lheywang/VolumeMixer/pcb/rev1/untitled.kicad_sch

## KiCad design pcb/rev1/untitled.kicad_sch (2025-06-10)

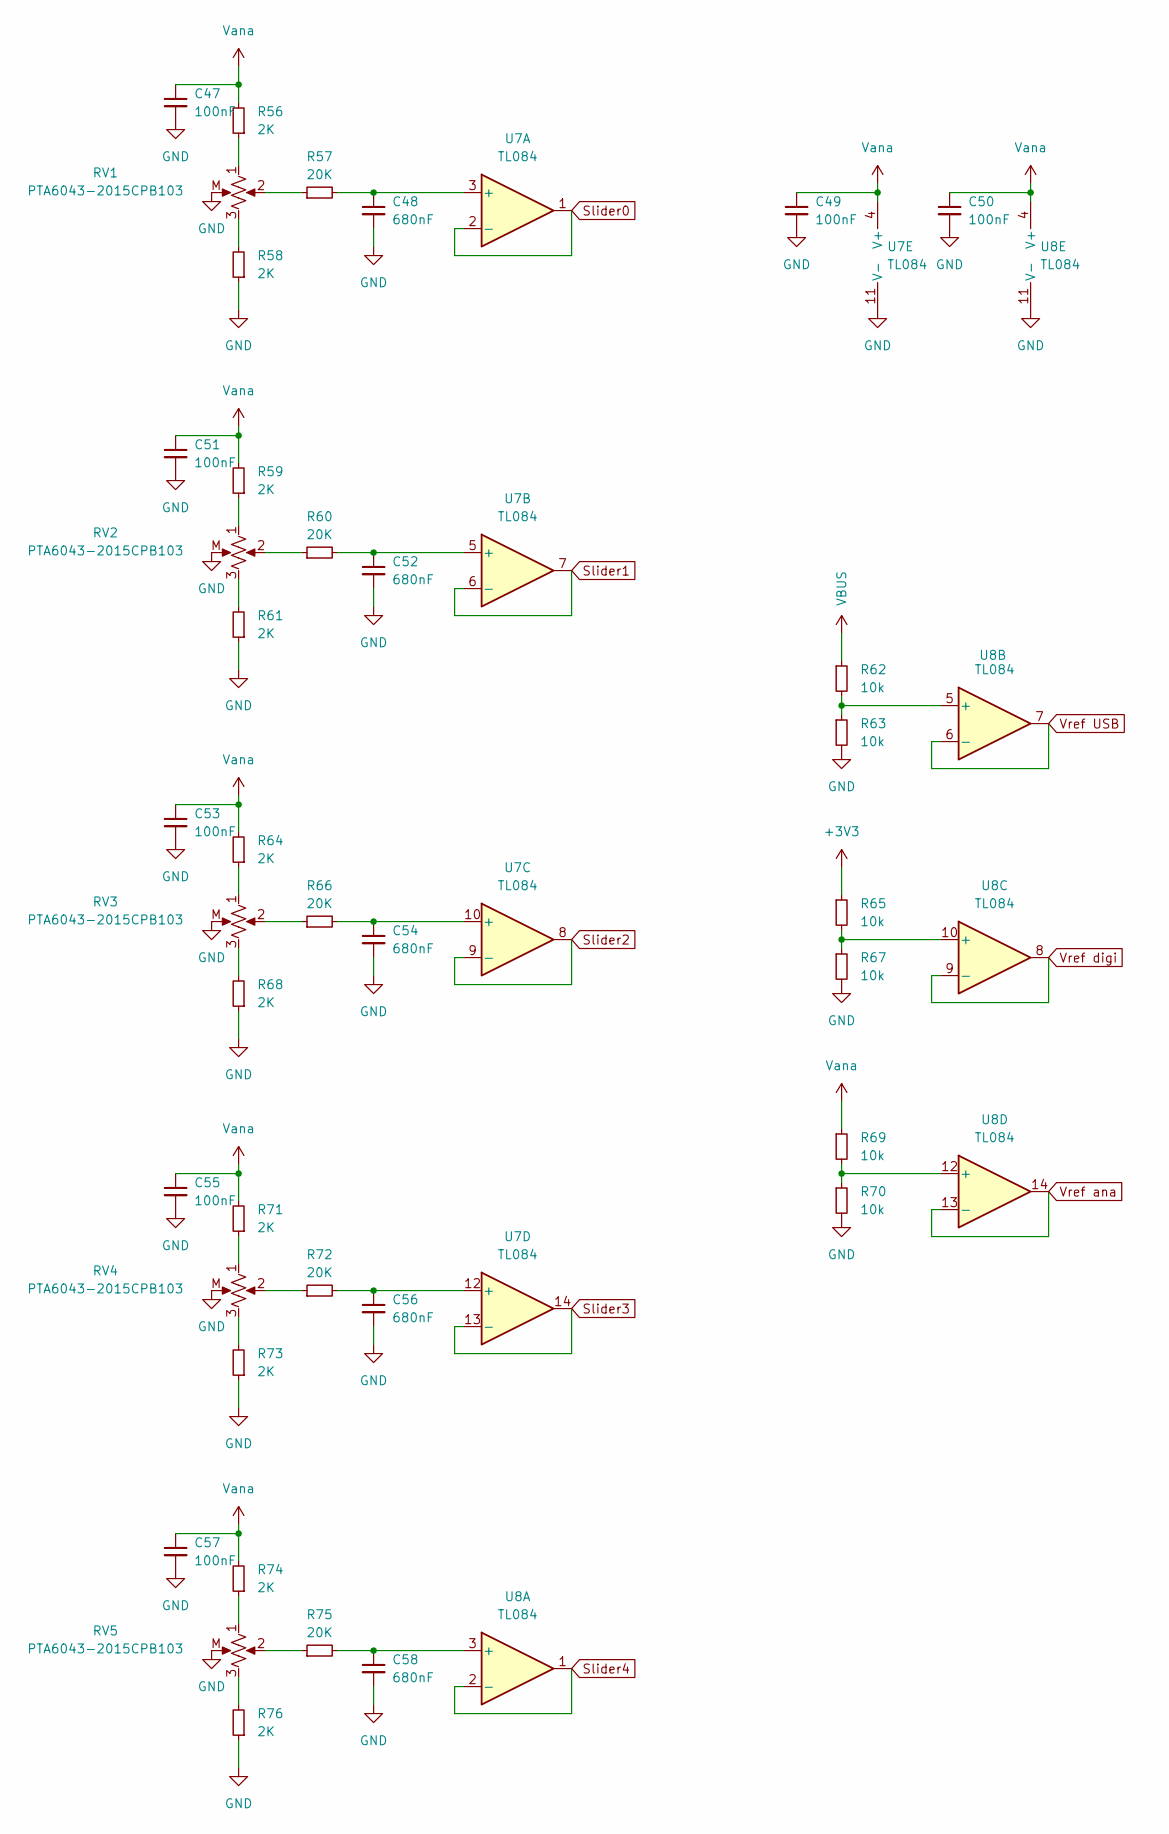
[picture p10: schematic untitled.kicad_sch]

Parts:
C47, C49, C50, C51, C53, C55, C57: 100nF; C_0603_1608Metric
C48, C52, C54, C56, C58: 680nF; C_0603_1608Metric
R56, R58, R59, R61, R64, R68, R71, R73, R74, R76: 2K; R_0603_1608Metric
R57, R60, R66, R72, R75: 20K; R_0603_1608Metric
R62, R63, R65, R67, R69, R70: 10k; R_0603_1608Metric
RV1, RV2, RV3, RV4, RV5: PTA6043-2015CPB103; Slider Bourns PTA6043-2015CPB103
U7, U8: TL084; SOIC-14_3.9x8.7mm_P1.27mm

Connections:
+3V3: R65.1
GND: C47.2, C48.2, C49.2, C50.2, C51.2, C52.2, C53.2, C54.2, C55.2, C56.2, C57.2, C58.2, R58.1, R61.1, R63.2, R67.2, R68.1, R70.2, R73.1, R76.1, RV1.M, RV2.M, RV3.M, RV4.M, RV5.M, U7.11 (V-), U8.11 (V-)
unnamed: C48.1, R57.2, U7.3 (+)
unnamed: C52.1, R60.2, U7.5 (+)
unnamed: C54.1, R66.2, U7.10 (+)
unnamed: C56.1, R72.2, U7.12 (+)
unnamed: C58.1, R75.2, U8.3 (+)
unnamed: R56.1, RV1.1
unnamed: R57.1, RV1.2
unnamed: R58.2, RV1.3
unnamed: R59.1, RV2.1
unnamed: R60.1, RV2.2
unnamed: R61.2, RV2.3
unnamed: R62.2, R63.1, U8.5 (+)
unnamed: R64.1, RV3.1
unnamed: R65.2, R67.1, U8.10 (+)
unnamed: R66.1, RV3.2
unnamed: R68.2, RV3.3
unnamed: R69.2, R70.1, U8.12 (+)
unnamed: R71.1, RV4.1
unnamed: R72.1, RV4.2
unnamed: R73.2, RV4.3
unnamed: R74.1, RV5.1
unnamed: R75.1, RV5.2
unnamed: R76.2, RV5.3
Slider0: U7.1, U7.2 (-)
Slider1: U7.6 (-), U7.7
Slider2: U7.8, U7.9 (-)
Slider3: U7.13 (-), U7.14
Slider4: U8.1, U8.2 (-)
VBUS: R62.1
Vana: C47.1, C49.1, C50.1, C51.1, C53.1, C55.1, C57.1, R56.2, R59.2, R64.2, R69.1, R71.2, R74.2, U7.4 (V+), U8.4 (V+)
Vref USB: U8.6 (-), U8.7
Vref ana: U8.13 (-), U8.14
Vref digi: U8.8, U8.9 (-)
