lheywang/VolumeMixer/pcb/rev1/volume-mixer.kicad_sch

## KiCad design pcb/rev1/volume-mixer.kicad_sch (2025-06-10)

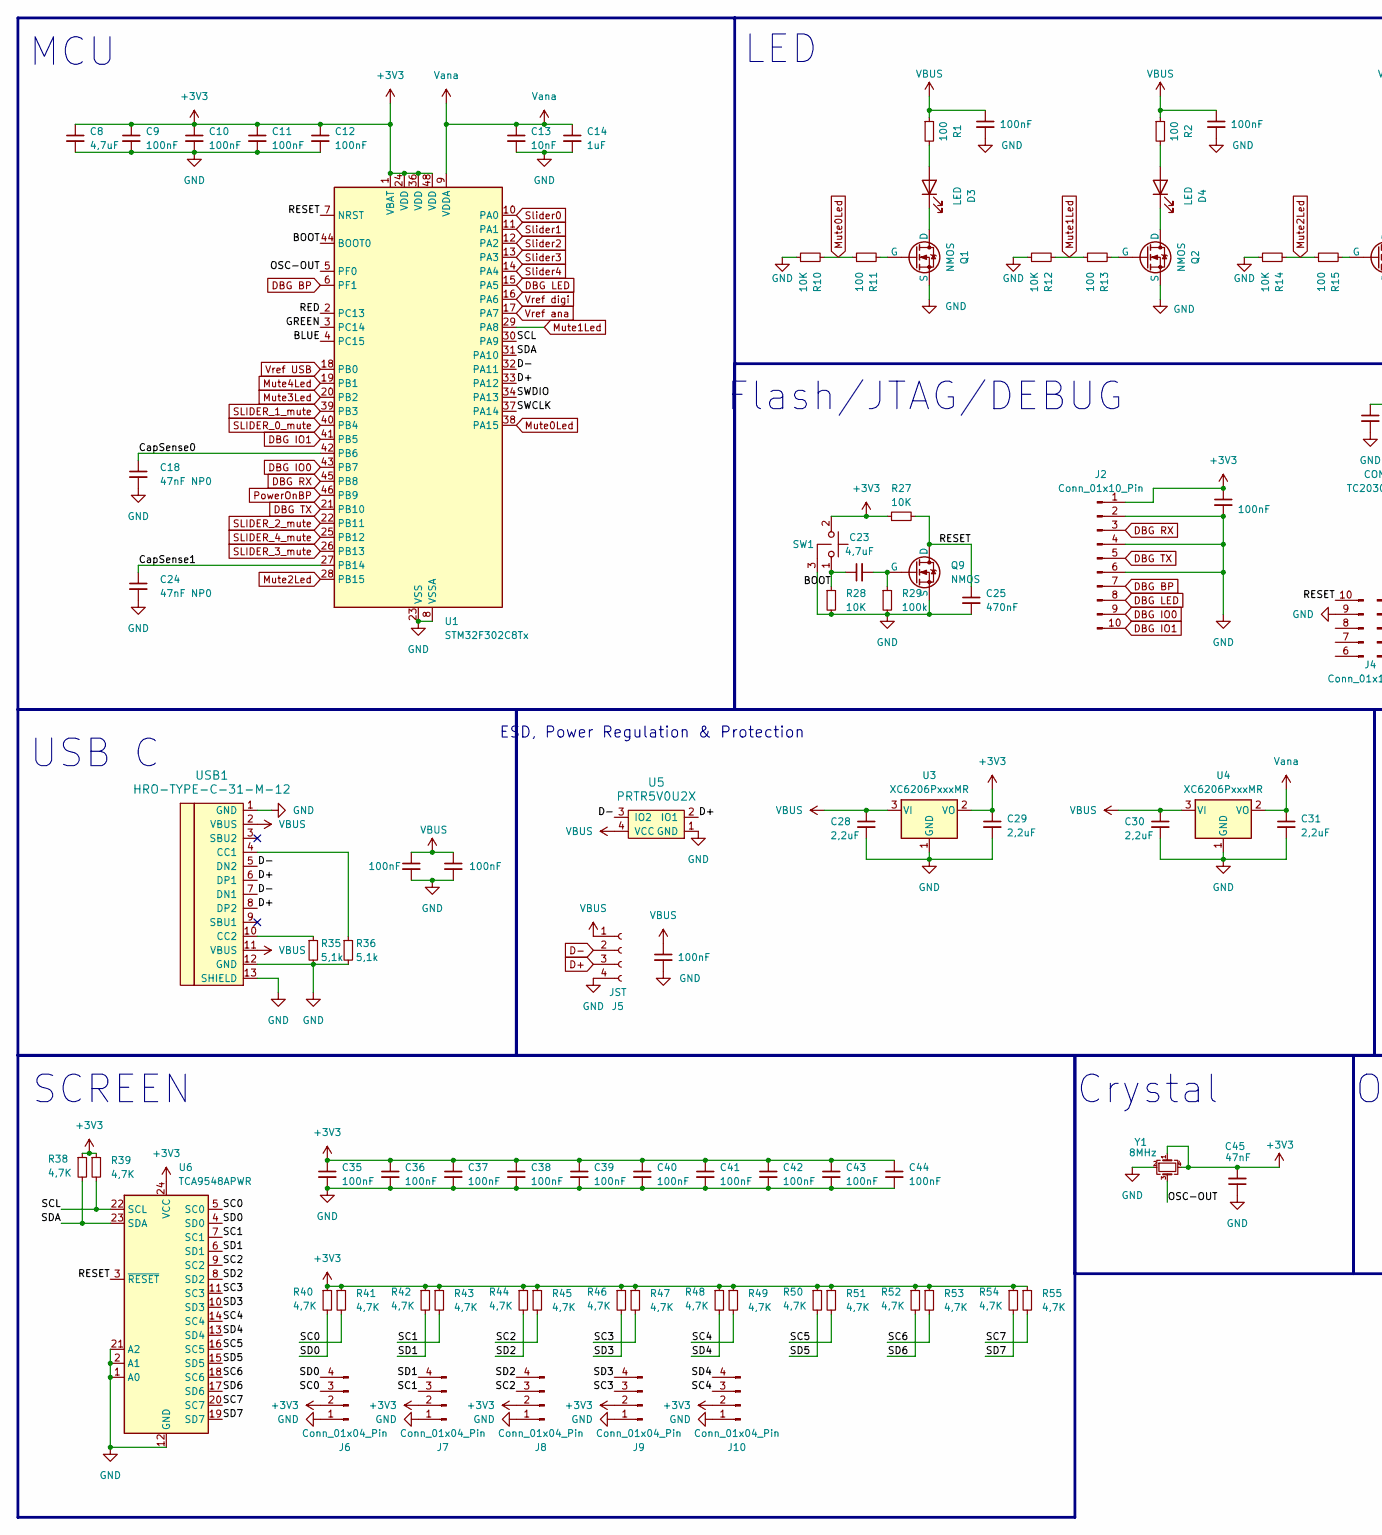
[picture p11: schematic volume-mixer.kicad_sch, part in row 1, column 1]

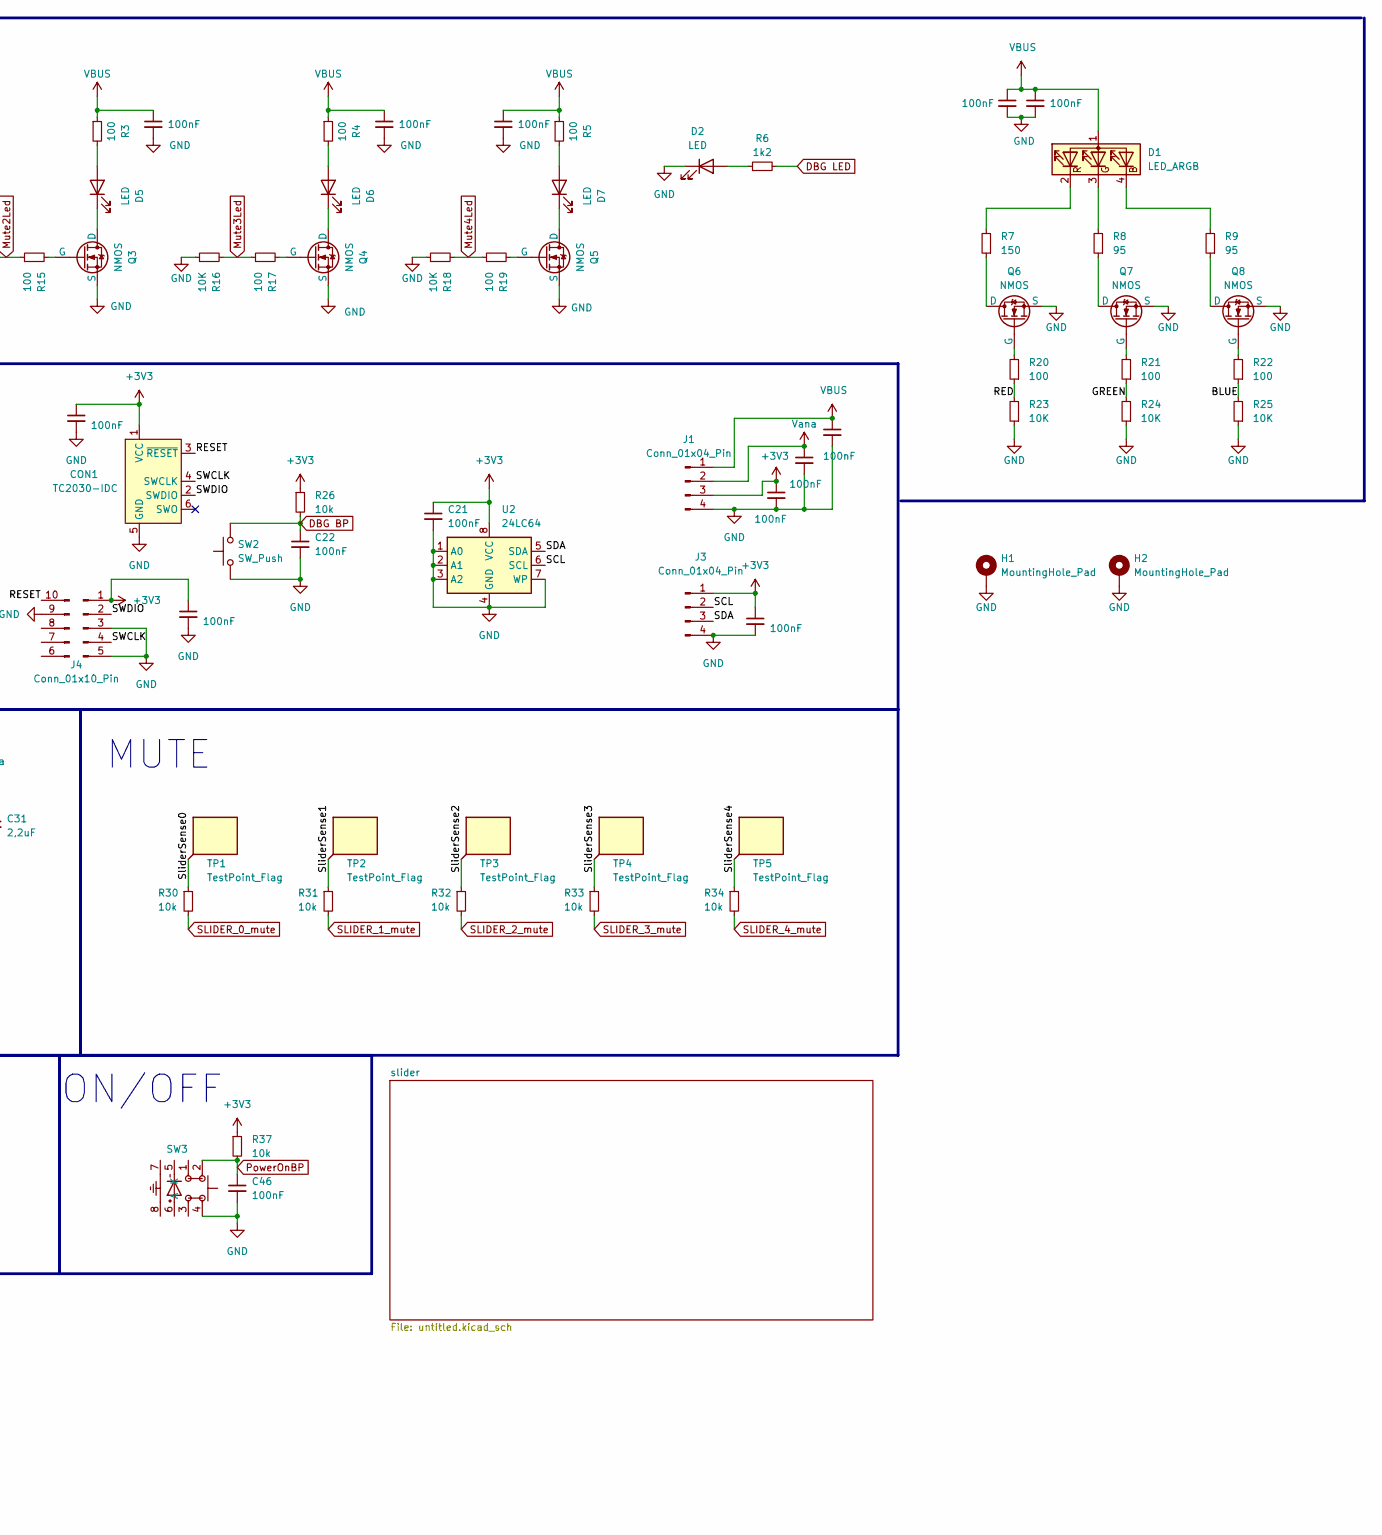
[picture p12: schematic volume-mixer.kicad_sch, part in row 1, column 2]

Parts:
C1, C2, C3, C4, C5, C6, C7, C9, C10, C11, C12, C15, C16, C17, C19, C20, C21, C22, C26, C27, C32, C33, C34, C35, C36, C37, C38, C39, C40, C41, C42, C43, C44, C46: 100nF; C_0603_1608Metric
C8, C23: 4,7uF; C_0603_1608Metric
C13: 10nF; C_0603_1608Metric
C14: 1uF; C_0603_1608Metric
C18, C24: 47nF NP0; C_0805_2012Metric
C25: 470nF; C_0603_1608Metric
C28, C29, C30, C31: 2,2uF; C_0603_1608Metric
C45: 47nF; C_0603_1608Metric
CON1: TC2030-IDC; Tag-Connect_TC2030-IDC-NL_2x03_P1.27mm_Vertical
D1: LED_ARGB; led rgb C7371893
D2: LED; LED_0805_2012Metric
D3, D4, D5, D6, D7: LED; LED C516299
H1, H2: MountingHole_Pad; Vis M2.5
J1, J3: Conn_01x04_Pin; PinHeader_1x04_P2.54mm_Vertical
J2: Conn_01x10_Pin; PinHeader_1x10_P2.54mm_Vertical
J4: Conn_01x10_Pin; PinHeader_2x05_P1.27mm_Vertical
J5: JST; JST-SR-4
J6, J7, J8, J9, J10: Conn_01x04_Pin; Screen 0.91 I2C
Q1, Q2, Q3, Q4, Q5, Q6, Q7, Q8, Q9: NMOS; SOT-23
R1, R2, R3, R4, R5, R11, R13, R15, R17, R19, R20, R21, R22: 100; R_0603_1608Metric
R6: 1k2; R_0603_1608Metric
R7: 150; R_0603_1608Metric
R8, R9: 95; R_0603_1608Metric
R10, R12, R14, R16, R18, R23, R24, R25, R27, R28: 10K; R_0603_1608Metric
R26, R30, R31, R32, R33, R34, R37: 10k; R_0603_1608Metric
R29: 100k; R_0603_1608Metric
R35, R36: 5,1k; R_0603_1608Metric
R38, R39, R40, R41, R42, R43, R44, R45, R46, R47, R48, R49, R50, R51, R52, R53, R54, R55: 4,7K; R_0603_1608Metric
SW1: switch C501547
SW2: SW_Push; SW_SPST_SKQG_WithStem
SW3: Sans titre
TP1, TP2, TP3, TP4, TP5: TestPoint_Flag; TestPoint_Keystone_5015_Micro_Mini
U1: STM32F302C8Tx; LQFP-48_7x7mm_P0.5mm
U2: 24LC64; SOIC-8_3.9x4.9mm_P1.27mm
U3, U4: XC6206PxxxMR; SOT-23-3
U5: PRTR5V0U2X; SOT-143
U6: TCA9548APWR; TSSOP-24_4.4x7.8mm_P0.65mm
USB1: HRO-TYPE-C-31-M-12
Y1: 8MHz; Crystal_SMD_2016-4Pin_2.0x1.6mm

Connections:
+3V3: C8.1, C9.1, C10.1, C11.1, C12.1, C15.1, C19.1, C20.1, C21.1, C26.1, C27.1, C29.1, C35.1, C36.1, C37.1, C38.1, C39.1, C40.1, C41.1, C42.1, C43.1, C44.1, C45.2, CON1.1 (VCC), J1.3, J2.1, J3.1, J4.1, J6.2, J7.2, J8.2, J9.2, J10.2, R26.1, R27.1, R37.1, R38.1, R39.1, R40.1, R41.1, R42.1, R43.1, R44.1, R45.1, R46.1, R47.1, R48.1, R49.1, R50.1, R51.1, R52.1, R53.1, R54.1, R55.1, SW1.2, U1.1 (VBAT), U1.24 (VDD), U1.36 (VDD), U1.48 (VDD), U2.8 (VCC), U3.2 (VO), U6.24 (VCC), Y1.1, Y1.4
BLUE: R22.1, R25.2, U1.4 (PC15)
BOOT: C23.1, R28.1, SW1.1, U1.44 (BOOT0)
CapSense0: C18.1, U1.42 (PB6)
CapSense1: C24.1, U1.27 (PB14)
D+: J5.3, U1.33 (PA12), U5.2 (IO1), USB1.6 (DP1), USB1.8 (DP2)
D-: J5.2, U1.32 (PA11), U5.3 (IO2), USB1.5 (DN2), USB1.7 (DN1)
DBG BP: C22.1, J2.7, R26.2, SW2.2, U1.6 (PF1)
DBG IO0: J2.9, U1.43 (PB7)
DBG IO1: J2.10, U1.41 (PB5)
DBG LED: J2.8, R6.2, U1.15 (PA5)
DBG RX: J2.3, U1.45 (PB8)
DBG TX: J2.5, U1.21 (PB10)
GND: C1.2, C2.2, C3.2, C4.2, C5.2, C6.2, C7.2, C8.2, C9.2, C10.2, C11.2, C12.2, C13.2, C14.2, C15.2, C16.2, C17.2, C18.2, C19.2, C20.2, C21.2, C22.2, C24.2, C25.2, C26.2, C27.2, C28.2, C29.2, C30.2, C31.2, C32.2, C33.2, C34.2, C35.2, C36.2, C37.2, C38.2, C39.2, C40.2, C41.2, C42.2, C43.2, C44.2, C45.1, C46.2, CON1.5 (GND), D2.1 (K), H1.1, H2.1, J1.4, J2.2, J2.4, J2.6, J3.4, J4.3, J4.5, J4.9, J5.4, J6.1, J7.1, J8.1, J9.1, J10.1, Q1.3 (S), Q2.3 (S), Q3.3 (S), Q4.3 (S), Q5.3 (S), Q6.3 (S), Q7.3 (S), Q8.3 (S), Q9.3 (S), R10.1, R12.1, R14.1, R16.1, R18.1, R23.1, R24.1, R25.1, R28.2, R29.2, R35.2, R36.2, SW1.3, SW2.1, SW3.4, U1.8 (VSSA), U1.23 (VSS), U1.35 (VSS), U1.47 (VSS), U2.1 (A0), U2.2 (A1), U2.3 (A2), U2.4 (GND), U2.7 (WP), U3.1 (GND), U4.1 (GND), U5.1 (GND), U6.1 (A0), U6.2 (A1), U6.12 (GND), U6.21 (A2), USB1.1 (GND), USB1.12 (GND), USB1.13 (SHIELD), Y1.2
GREEN: R21.1, R24.2, U1.3 (PC14)
Mute0Led: R10.2, R11.1, U1.38 (PA15)
Mute1Led: R12.2, R13.1, U1.29 (PA8)
Mute2Led: R14.2, R15.1, U1.28 (PB15)
Mute3Led: R16.2, R17.1, U1.20 (PB2)
Mute4Led: R18.2, R19.1, U1.19 (PB1)
unnamed: C23.2, Q9.2 (G), R29.1
unnamed: D1.2 (RK), R7.2
unnamed: D1.3 (GK), R8.2
unnamed: D1.4 (BK), R9.2
unnamed: D2.2 (A), R6.1
unnamed: D3.1 (K), Q1.1 (D)
unnamed: D3.2 (A), R1.2
unnamed: D4.1 (K), Q2.1 (D)
unnamed: D4.2 (A), R2.2
unnamed: D5.1 (K), Q3.1 (D)
unnamed: D5.2 (A), R3.2
unnamed: D6.1 (K), Q4.1 (D)
unnamed: D6.2 (A), R4.2
unnamed: D7.1 (K), Q5.1 (D)
unnamed: D7.2 (A), R5.2
unnamed: Q1.2 (G), R11.2
unnamed: Q2.2 (G), R13.2
unnamed: Q3.2 (G), R15.2
unnamed: Q4.2 (G), R17.2
unnamed: Q5.2 (G), R19.2
unnamed: Q6.1 (D), R7.1
unnamed: Q6.2 (G), R20.2
unnamed: Q7.1 (D), R8.1
unnamed: Q7.2 (G), R21.2
unnamed: Q8.1 (D), R9.1
unnamed: Q8.2 (G), R22.2
unnamed: R35.1, USB1.10 (CC2)
unnamed: R36.1, USB1.4 (CC1)
OSC-OUT: U1.5 (PF0), Y1.3
PowerOnBP: C46.1, R37.2, SW3.2, U1.46 (PB9)
RED: R20.1, R23.2, U1.2 (PC13)
RESET: C25.1, CON1.3 (~RESET), J4.10, Q9.1 (D), R27.2, U1.7 (NRST), U6.3 (~RESET)
SC0: J6.3, R41.2, U6.5 (SC0)
SC1: J7.3, R43.2, U6.7 (SC1)
SC2: J8.3, R45.2, U6.9 (SC2)
SC3: J9.3, R47.2, U6.11 (SC3)
SC4: J10.3, R49.2, U6.14 (SC4)
SC5: R51.2, U6.16 (SC5)
SC6: R53.2, U6.18 (SC6)
SC7: R55.2, U6.20 (SC7)
SCL: J3.2, R39.2, U1.30 (PA9), U2.6 (SCL), U6.22 (SCL)
SD0: J6.4, R40.2, U6.4 (SD0)
SD1: J7.4, R42.2, U6.6 (SD1)
SD2: J8.4, R44.2, U6.8 (SD2)
SD3: J9.4, R46.2, U6.10 (SD3)
SD4: J10.4, R48.2, U6.13 (SD4)
SD5: R50.2, U6.15 (SD5)
SD6: R52.2, U6.17 (SD6)
SD7: R54.2, U6.19 (SD7)
SDA: J3.3, R38.2, U1.31 (PA10), U2.5 (SDA), U6.23 (SDA)
SLIDER_0_mute: R30.2, U1.40 (PB4)
SLIDER_1_mute: R31.2, U1.39 (PB3)
SLIDER_2_mute: R32.2, U1.22 (PB11)
SLIDER_3_mute: R33.2, U1.26 (PB13)
SLIDER_4_mute: R34.2, U1.25 (PB12)
SWCLK: CON1.4 (SWCLK), J4.4, U1.37 (PA14)
SWDIO: CON1.2 (SWDIO), J4.2, U1.34 (PA13)
Slider0: U1.10 (PA0)
Slider1: U1.11 (PA1)
Slider2: U1.12 (PA2)
Slider3: U1.13 (PA3)
Slider4: U1.14 (PA4)
SliderSense0: R30.1, TP1.1
SliderSense1: R31.1, TP2.1
SliderSense2: R32.1, TP3.1
SliderSense3: R33.1, TP4.1
SliderSense4: R34.1, TP5.1
VBUS: C1.1, C2.1, C3.1, C4.1, C5.1, C6.1, C7.1, C16.1, C28.1, C30.1, C32.1, C33.1, C34.1, D1.1 (A), J1.1, J5.1, R1.1, R2.1, R3.1, R4.1, R5.1, U3.3 (VI), U4.3 (VI), U5.4 (VCC), USB1.2 (VBUS), USB1.11 (VBUS)
Vana: C13.1, C14.1, C17.1, C31.1, J1.2, U1.9 (VDDA), U4.2 (VO)
Vref USB: U1.18 (PB0)
Vref ana: U1.17 (PA7)
Vref digi: U1.16 (PA6)

Notes on the sheet:
SCREEN
ESD, Power Regulation & Protection
USB C
ON/OFF
MCU
Crystal
LED
Flash/JTAG/DEBUG
MUTE
