lheywang/VolumeMixer/code/host/host/host/dev/device.py

# ==============================================================================
#   host/dev/device.py :    Implement the device class, used to send and read
#                           commands.
#
#   10/06/2025
#   l.heywang <leonard.heywang@proton.me>
#
# ==============================================================================

# ------------------------------------------------------------------------------
# Importing modules
# ------------------------------------------------------------------------------
import serial
import serial.serialutil
import serial.tools.list_ports
import time
import logging

# ------------------------------------------------------------------------------
# Local imports
# ------------------------------------------------------------------------------
from . import IsDeviceAvailable, IsCommandValid, GetCommandStatus
from . import CmdASYNC, CmdDCONF, CmdSLPOS, CmdUICON, CmdCONNC, CmdRINIT, CmdSHUTD

# ------------------------------------------------------------------------------
# Defining some constants
# ------------------------------------------------------------------------------
BAUD = 921600
BYTE = serial.EIGHTBITS
PARITY = serial.PARITY_NONE
STOP = serial.STOPBITS_ONE


# ------------------------------------------------------------------------------
# Defining the base class
# ------------------------------------------------------------------------------


class MixerDevice:

    def __init__(self, logger: logging.Logger) -> None:
        self.logger = logger

        # First, choose the COM port and set the launch guard to prevent any IO on unconfigured com port.
        # Todo : Uncomment this for real working !
        if self._SelectCOMPort() != 0:
            self.logger.error("No device available. Exiting...")
            self.IsDeviceOpenned = False
            return
        self.logger.info(f"Found a VolumeMixer device on port : {self.port.port}")
        self.IsDeviceOpenned = True

        # Then, we've got a device, so we try to connect to it
        cmd = CmdCONNC()
        self.IsDeviceConnected = self.SendCommand(cmd)

        if self.IsDeviceConnected:
            self.logger.info("Connected to device !")
        else:
            self.logger.error("Connected refused to device")

    def _SelectCOMPort(self):
        """
            Attempts to automatically select and open a serial COM port connected to a compatible mixer device.
            This method scans all available serial ports, tries to open each one, and reads initial data to determine
            if the connected device is a mixer ready to accept a connection. If a suitable device is found, the serial
            port is assigned to `self.port` and the method returns 0. If no compatible device is found, returns -1.

        Returns:
            int: 0 if a compatible device is found and the port is opened, -1 otherwise.

        Raises:
            Exception: If an unhandled error occurs while opening a port.
        """
        # First, list all of the available serial ports
        ports = list(serial.tools.list_ports.comports())

        # Then, try to open the ports and see if something is fetched ?:?

        for port in ports:
            try:
                self.logger.info(f"Trying port {port.name} ...")
                tmp = serial.Serial(
                    port.name,
                    baudrate=BAUD,
                    bytesize=BYTE,
                    parity=PARITY,
                    stopbits=STOP,
                    timeout=1.0,
                )
            # Unable to open com port
            except serial.serialutil.SerialException:
                continue
            except Exception as e:
                raise Exception(f"Unhandled error : {e}")

            # Then, if the port was openned, wait for a read operation : (message every 500 ms).
            time.sleep(0.6)

            try:
                data = tmp.read(tmp.in_waiting).decode()

                # Check if the message is typical from a mixer ready to accept a connection
                if IsDeviceAvailable(data):
                    self.port = tmp
                    self.logger.info(f"Found a device on : {self.port.port} !")
                    return 0
                else:
                    continue
            except UnicodeDecodeError as e:
                self.logger.info(f"Could not decode COM port {tmp.port} : {e}")
                continue

        return -1

    def SendCommand(
        self,
        cmd: CmdASYNC | CmdDCONF | CmdSLPOS | CmdUICON | CmdCONNC | CmdRINIT | CmdSHUTD,
    ):
        # First, get the command :
        buf = cmd.cmd()
        self.logger.debug(f"Sending buffer : {buf}")

        # Then, write the command on the serial port
        if self.IsDeviceOpenned:
            self.port.write(buf.encode())

            # Immediately return, True, because theses commands will
            # trigger the target in mode where it CAN'T respond...
            if type(cmd) == CmdRINIT or type(cmd) == CmdSHUTD:
                return cmd, True

            # Wait for an END tocken to be found to be seen.
            # The input buffer is flushed, to ensure no error will be fetched.
            self.port.reset_input_buffer()
            tmp = self.port.read_until(";END").decode().strip().strip("\0")
            self.logger.debug(f"Rode from the device : {tmp}")

            # Parse the output
            valid = IsCommandValid(tmp)
            if not valid:
                self.logger.warning(
                    f"Invalid command was received (False CRC). Ignoring it..."
                )
                return cmd, False

            # Check the return value of the command
            if type(cmd) == CmdASYNC or type(cmd) == CmdSLPOS:
                cmd.parse(tmp.split(";")[3])
                return cmd, True
            else:
                return cmd, GetCommandStatus(tmp)

        return cmd, False
